rectifiedtech/Rick-Flash/Arduino Code/Rick_Flash/data/rick.gif

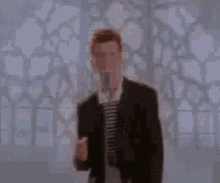
Arduino Code/Rick_Flash/data/rick.gif
